sporniket/kicad-conversions--thomson-mo5--v1/references/motherboard/bottom-reversed.png

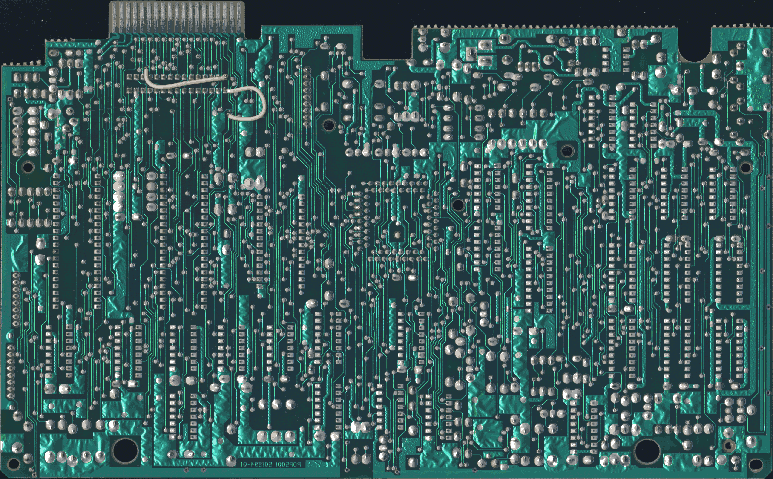
references/motherboard/bottom-reversed.png
