sporniket/kicad-conversions--thomson-mo5--v1/references/motherboard/pictures_top/DSC_1524.JPG

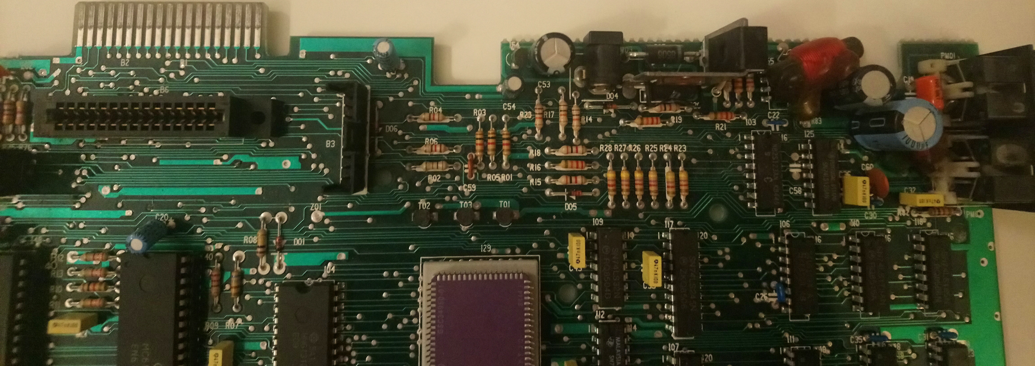
references/motherboard/pictures_top/DSC_1524.JPG
