sporniket/kicad-conversions--thomson-mo5--v1/references/motherboard/pictures_top/DSC_1542.JPG

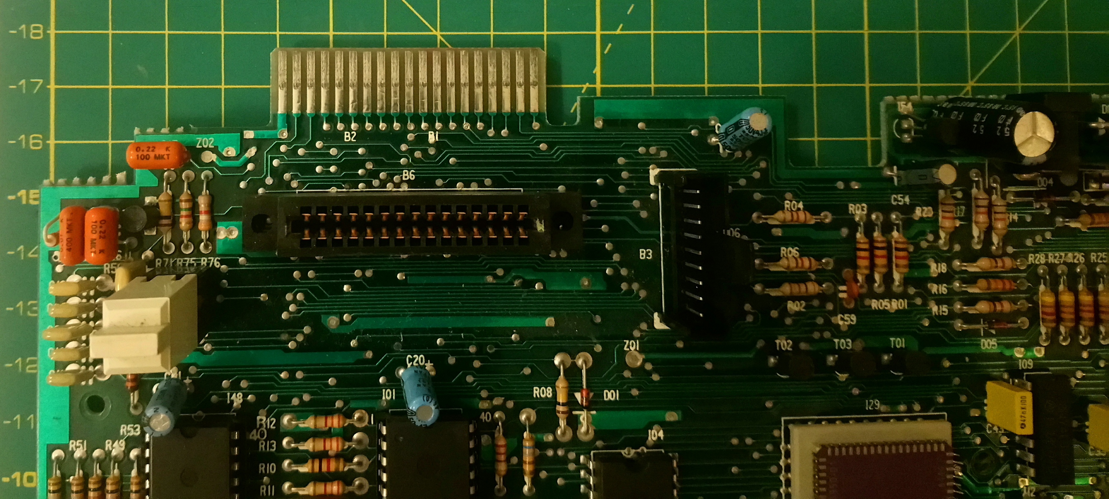
references/motherboard/pictures_top/DSC_1542.JPG
