sporniket/kicad-conversions--thomson-mo5--v1/references/motherboard/pictures_top/DSC_1543.JPG

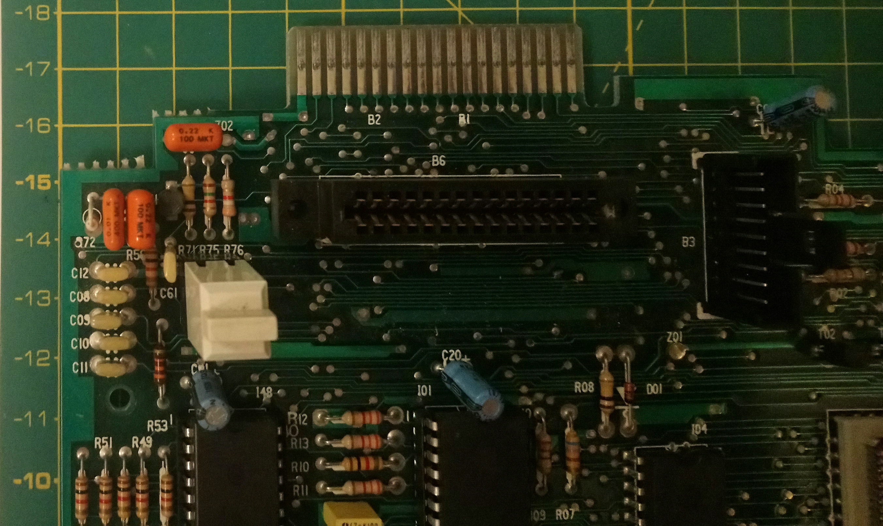
references/motherboard/pictures_top/DSC_1543.JPG
