sporniket/kicad-conversions--thomson-mo5--v1/references/motherboard/top.png

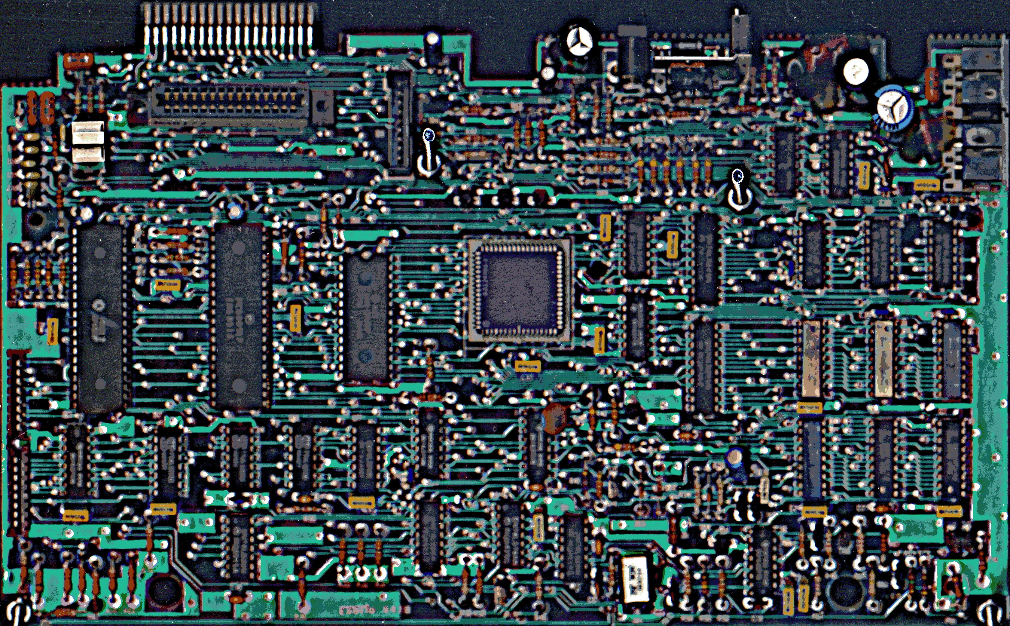
references/motherboard/top.png
