sporniket/kicad-conversions--thomson-mo5--v1/subsheet_100.kicad_sch

## KiCad design subsheet_100.kicad_sch (2025-02-01, an earlier design)

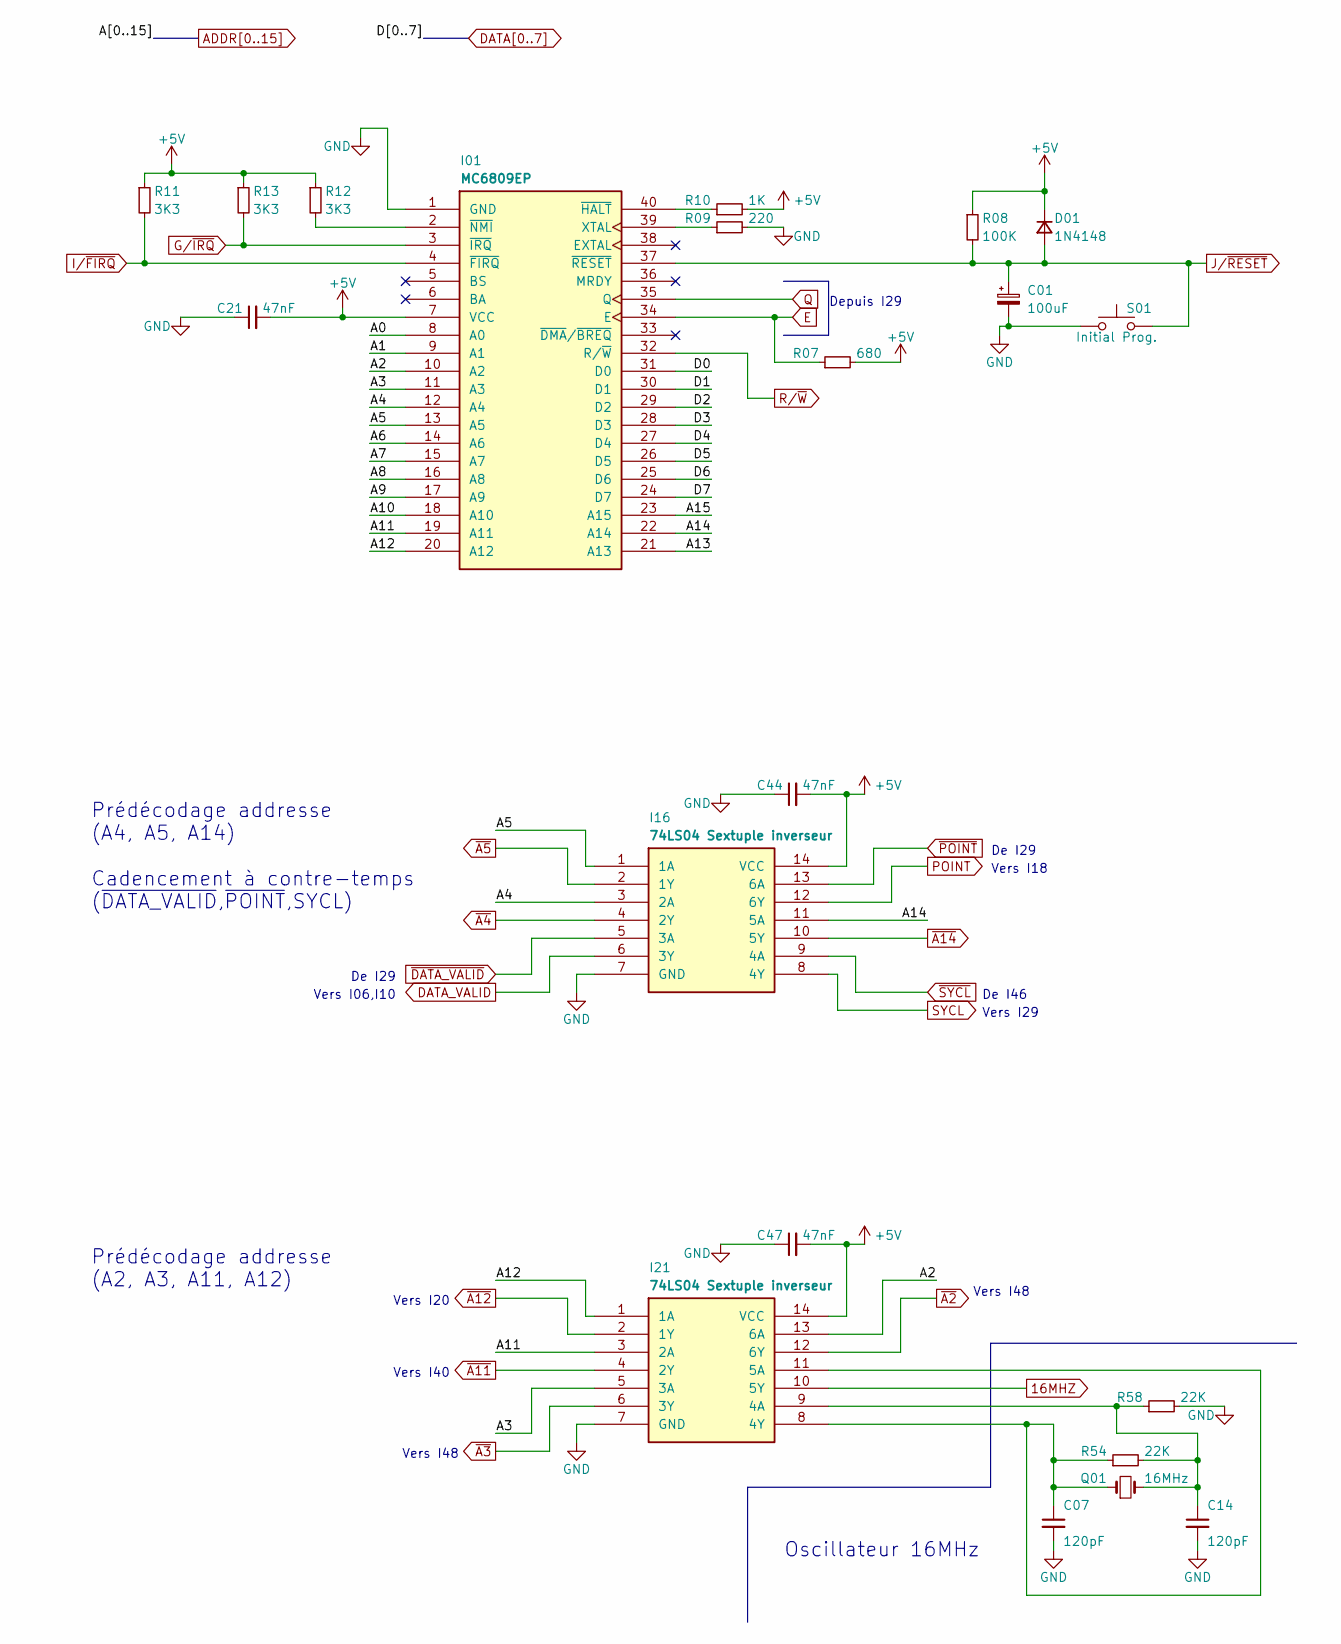
[picture p26: schematic subsheet_100.kicad_sch]

Parts:
C01: 100uF; Passive_THT_capacitor_polarized_EU_W2.54mm_L5.08mm
C07, C14: 120pF; Passive_THT_capacitor_mlcc_W2.54mm_L5.08mm
C21, C44, C47: 47nF; Passive_THT_capacitor_mlcc_W2.54mm_L5.08mm
D01: 1N4148; Passive_THT_diode_W2.54mm_L12.70mm
I01: MC6809EP; DIP-40_W15.24mm_LongPads
I16, I21: 74LS04 Sextuple inverseur; DIP-14_W7.62mm_LongPads
Q01: 16MHz
R07: 680; Passive_THT_resistor_EU_W2.54mm_L12.70mm
R08: 100K; Passive_THT_resistor_EU_W2.54mm_L12.70mm
R09: 220; Passive_THT_resistor_EU_W2.54mm_L12.70mm
R10: 1K; Passive_THT_resistor_EU_W2.54mm_L12.70mm
R11, R12, R13: 3K3; Passive_THT_resistor_EU_W2.54mm_L12.70mm
R54, R58: 22K; Passive_THT_resistor_EU_W2.54mm_L12.70mm
S01: Initial Prog.

Connections:
16MHZ: I21.10 (5Y)
+5V: C21.2, C44.2, C47.2, D01.1 (K), I01.7 (VCC), I16.14 (VCC), I21.14 (VCC), R07.2, R08.1, R10.2, R11.1, R12.1, R13.1
A0: I01.8 (A0)
A1: I01.9 (A1)
A2: I01.10 (A2), I21.13 (6A)
A3: I01.11 (A3), I21.5 (3A)
A4: I01.12 (A4), I16.3 (2A)
A5: I01.13 (A5), I16.1 (1A)
A6: I01.14 (A6)
A7: I01.15 (A7)
A8: I01.16 (A8)
A9: I01.17 (A9)
A10: I01.18 (A10)
A11: I01.19 (A11), I21.3 (2A)
A12: I01.20 (A12), I21.1 (1A)
A13: I01.21 (A13)
A14: I01.22 (A14), I16.11 (5A)
A15: I01.23 (A15)
D0: I01.31 (D0)
D1: I01.30 (D1)
D2: I01.29 (D2)
D3: I01.28 (D3)
D4: I01.27 (D4)
D5: I01.26 (D5)
D6: I01.25 (D6)
D7: I01.24 (D7)
DATA_VALID: I16.6 (3Y)
E: I01.34 (E), R07.1
GND: C01.2, C07.2, C14.2, C21.1, C44.1, C47.1, I01.1 (GND), I16.7 (GND), I21.7 (GND), R09.2, R58.2, S01.1
G/~IRQ: I01.3 (~IRQ), R13.2
I/~FIRQ: I01.4 (~FIRQ), R11.2
J/~RESET: C01.1, D01.2 (A), I01.37 (~RESET), R08.2, S01.2
unnamed: C07.1, I21.8 (4Y), I21.11 (5A), Q01.1, R54.1
unnamed: C14.1, I21.9 (4A), Q01.2, R54.2, R58.1
unnamed: I01.2 (~NMI), R12.2
unnamed: I01.39 (XTAL), R09.1
unnamed: I01.40 (~HALT), R10.1
POINT: I16.12 (6Y)
Q: I01.35 (Q)
R/~W: I01.32 (R/~W)
SYCL: I16.8 (4Y)
~A2: I21.12 (6Y)
~A3: I21.6 (3Y)
~A4: I16.4 (2Y)
~A5: I16.2 (1Y)
~A11: I21.4 (2Y)
~A12: I21.2 (1Y)
~A14: I16.10 (5Y)
~DATA_VALID: I16.5 (3A)
~POINT: I16.13 (6A)
~SYCL: I16.9 (4A)

Notes on the sheet:
De I46
Vers I29
Vers I48
Vers I20
Oscillateur 16MHz
De I29
Prédécodage addresse (A2, A3, A11, A12)
Vers I06,I10
Vers I40
Prédécodage addresse (A4, A5, A14) Cadencement à contre-temps (~{DATA_VALID},~{POINT},SYCL)
Depuis I29
Vers I18
