sporniket/kicad-conversions--thomson-mo5--v1/subsheet_101.kicad_sch

## KiCad design subsheet_101.kicad_sch (2024-12-30, an earlier design)

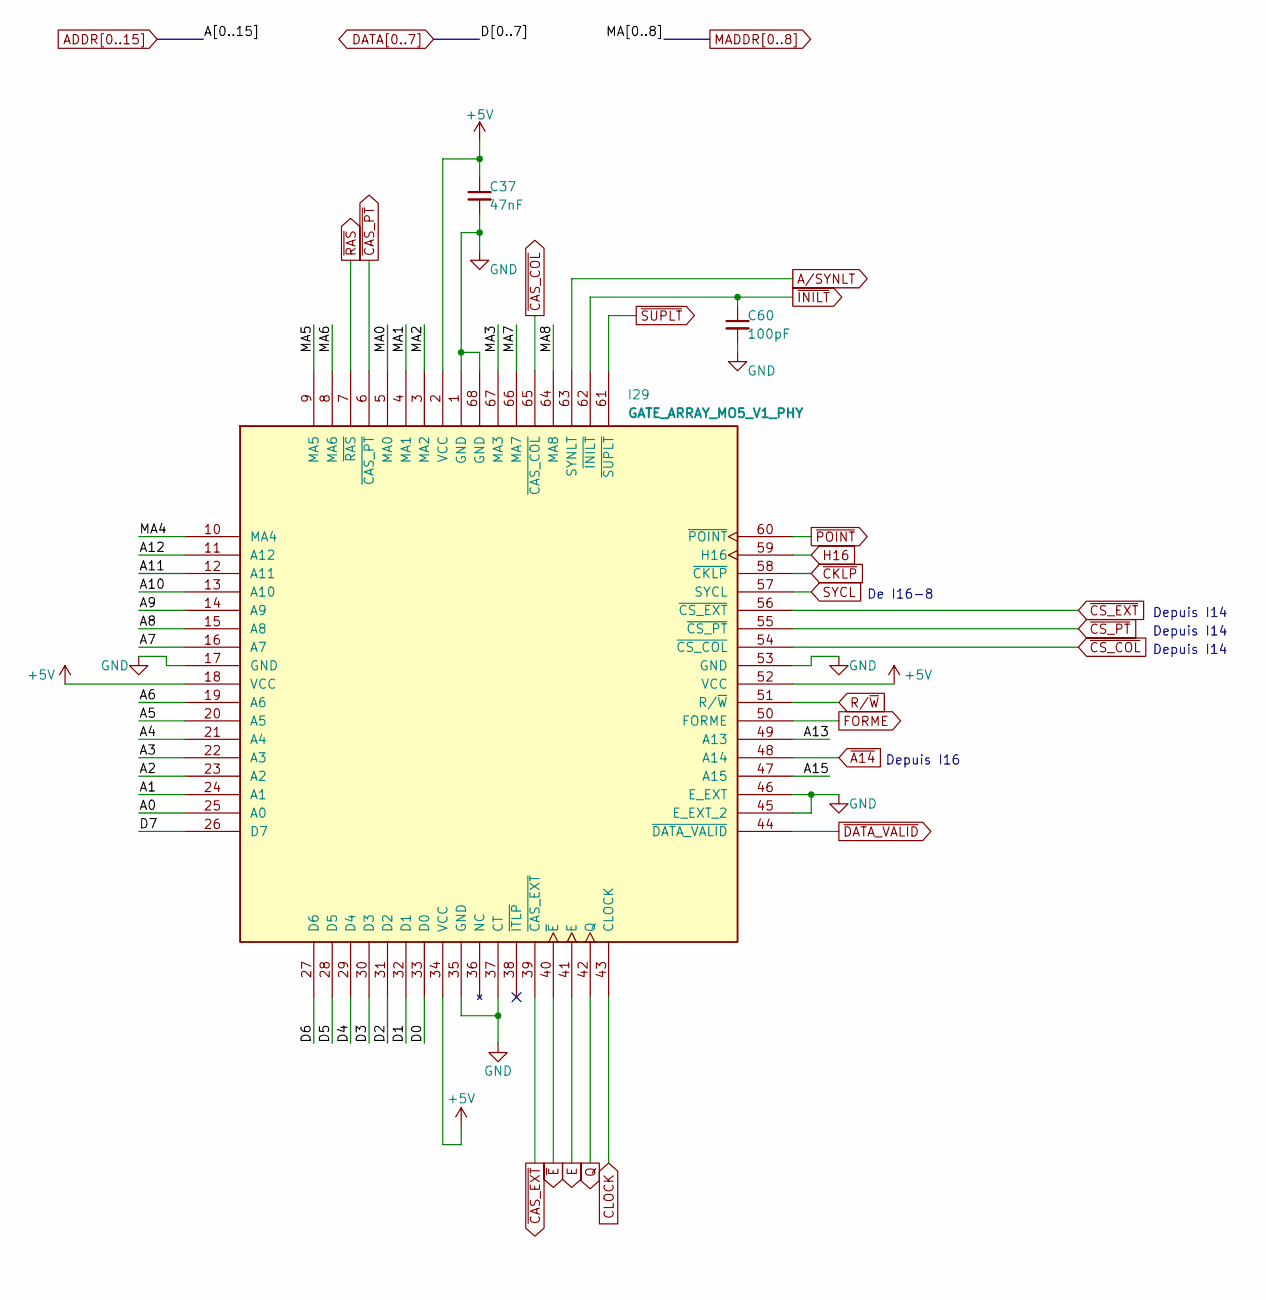
[picture p27: schematic subsheet_101.kicad_sch]

Parts:
C37: 47nF; Passive_THT_capacitor_mlcc_W2.54mm_L5.08mm
C60: 100pF; Passive_THT_capacitor_mlcc_W2.54mm_L5.08mm
I29: GATE_ARRAY_MO5_V1_PHY; gate_array_plcc68_staggered_with_key_hole

Connections:
+5V: C37.1, I29.2 (VCC), I29.18 (VCC), I29.34 (VCC), I29.52 (VCC)
A0: I29.25 (A0)
A1: I29.24 (A1)
A2: I29.23 (A2)
A3: I29.22 (A3)
A4: I29.21 (A4)
A5: I29.20 (A5)
A6: I29.19 (A6)
A7: I29.16 (A7)
A8: I29.15 (A8)
A9: I29.14 (A9)
A10: I29.13 (A10)
A11: I29.12 (A11)
A12: I29.11 (A12)
A13: I29.49 (A13)
A15: I29.47 (A15)
A/SYNLT: I29.63 (SYNLT)
CLOCK: I29.43 (CLOCK)
D0: I29.33 (D0)
D1: I29.32 (D1)
D2: I29.31 (D2)
D3: I29.30 (D3)
D4: I29.29 (D4)
D5: I29.28 (D5)
D6: I29.27 (D6)
D7: I29.26 (D7)
E: I29.41 (E)
FORME: I29.50 (FORME)
GND: C37.2, C60.2, I29.1 (GND), I29.17 (GND), I29.35 (GND), I29.37 (CT), I29.45 (E_EXT_2), I29.46 (E_EXT), I29.53 (GND), I29.68 (GND)
H16: I29.59 (H16)
MA0: I29.5 (MA0)
MA1: I29.4 (MA1)
MA2: I29.3 (MA2)
MA3: I29.67 (MA3)
MA4: I29.10 (MA4)
MA5: I29.9 (MA5)
MA6: I29.8 (MA6)
MA7: I29.66 (MA7)
MA8: I29.64 (MA8)
Q: I29.42 (Q)
R/~W: I29.51 (R/~W)
SYCL: I29.57 (SYCL)
~A14: I29.48 (A14)
~CAS_COL: I29.65 (~CAS_COL)
~CAS_EXT: I29.39 (~CAS_EXT)
~CAS_PT: I29.6 (~CAS_PT)
~CKLP: I29.58 (~CKLP)
~CS_COL: I29.54 (~CS_COL)
~CS_EXT: I29.56 (~CS_EXT)
~CS_PT: I29.55 (~CS_PT)
~DATA_VALID: I29.44 (~DATA_VALID)
~E: I29.40 (~E)
~INILT: C60.1, I29.62 (~INILT)
~POINT: I29.60 (~POINT)
~RAS: I29.7 (~RAS)
~SUPLT: I29.61 (~SUPLT)

Notes on the sheet:
Depuis I14
Depuis I16
De I16-8
