sporniket/kicad-conversions--thomson-mo5--v1/subsheet_102.kicad_sch

## KiCad design subsheet_102.kicad_sch (2024-12-30, an earlier design)

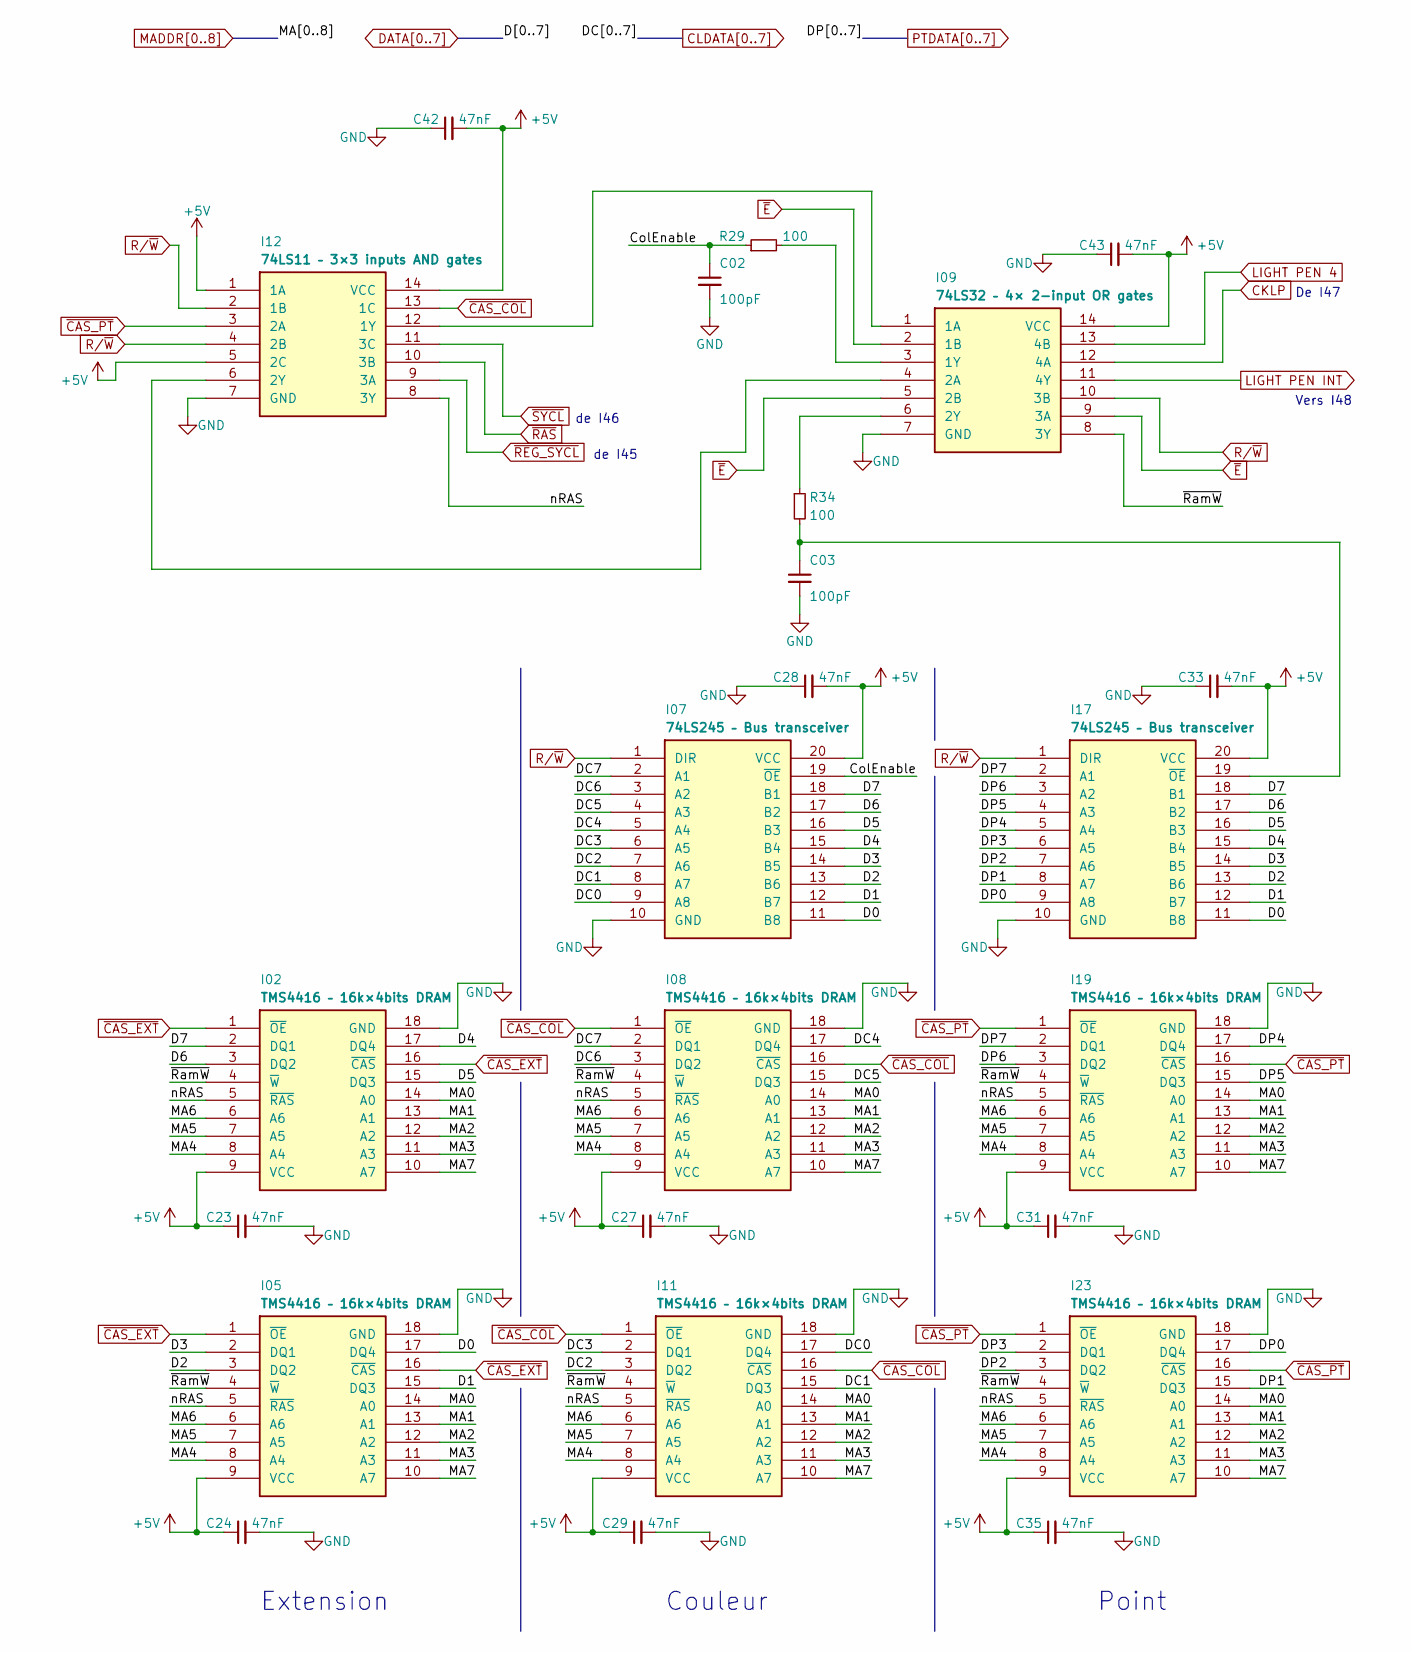
[picture p28: schematic subsheet_102.kicad_sch]

Parts:
C02, C03: 100pF; Passive_THT_capacitor_mlcc_W2.54mm_L5.08mm
C23, C24, C27, C28, C29, C31, C33, C35, C42, C43: 47nF; Passive_THT_capacitor_mlcc_W2.54mm_L5.08mm
I02, I05, I08, I11, I19, I23: TMS4416 – 16k×4bits DRAM; DIP-18_W7.62mm_LongPads
I07, I17: 74LS245 – Bus transceiver; DIP-20_W7.62mm_LongPads
I09: 74LS32 – 4× 2-input OR gates; DIP-14_W7.62mm_LongPads
I12: 74LS11 – 3×3 inputs AND gates; DIP-14_W7.62mm_LongPads
R29, R34: 100; Passive_THT_resistor_EU_W2.54mm_L12.70mm

Connections:
+5V: C23.1, C24.1, C27.1, C28.2, C29.1, C31.1, C33.2, C35.1, C42.2, C43.2, I02.9 (VCC), I05.9 (VCC), I07.20 (VCC), I08.9 (VCC), I09.14 (VCC), I11.9 (VCC), I12.1 (1A), I12.5 (2C), I12.14 (VCC), I17.20 (VCC), I19.9 (VCC), I23.9 (VCC)
CKLP: I09.12 (4A)
ColEnable: C02.1, I07.19 (~OE), R29.1
D0: I05.17 (DQ4), I07.11 (B8), I17.11 (B8)
D1: I05.15 (DQ3), I07.12 (B7), I17.12 (B7)
D2: I05.3 (DQ2), I07.13 (B6), I17.13 (B6)
D3: I05.2 (DQ1), I07.14 (B5), I17.14 (B5)
D4: I02.17 (DQ4), I07.15 (B4), I17.15 (B4)
D5: I02.15 (DQ3), I07.16 (B3), I17.16 (B3)
D6: I02.3 (DQ2), I07.17 (B2), I17.17 (B2)
D7: I02.2 (DQ1), I07.18 (B1), I17.18 (B1)
DC0: I07.9 (A8), I11.17 (DQ4)
DC1: I07.8 (A7), I11.15 (DQ3)
DC2: I07.7 (A6), I11.3 (DQ2)
DC3: I07.6 (A5), I11.2 (DQ1)
DC4: I07.5 (A4), I08.17 (DQ4)
DC5: I07.4 (A3), I08.15 (DQ3)
DC6: I07.3 (A2), I08.3 (DQ2)
DC7: I07.2 (A1), I08.2 (DQ1)
DP0: I17.9 (A8), I23.17 (DQ4)
DP1: I17.8 (A7), I23.15 (DQ3)
DP2: I17.7 (A6), I23.3 (DQ2)
DP3: I17.6 (A5), I23.2 (DQ1)
DP4: I17.5 (A4), I19.17 (DQ4)
DP5: I17.4 (A3), I19.15 (DQ3)
DP6: I17.3 (A2), I19.3 (DQ2)
DP7: I17.2 (A1), I19.2 (DQ1)
GND: C02.2, C03.2, C23.2, C24.2, C27.2, C28.1, C29.2, C31.2, C33.1, C35.2, C42.1, C43.1, I02.18 (GND), I05.18 (GND), I07.10 (GND), I08.18 (GND), I09.7 (GND), I11.18 (GND), I12.7 (GND), I17.10 (GND), I19.18 (GND), I23.18 (GND)
LIGHT PEN 4: I09.13 (4B)
LIGHT PEN INT: I09.11 (4Y)
MA0: I02.14 (A0), I05.14 (A0), I08.14 (A0), I11.14 (A0), I19.14 (A0), I23.14 (A0)
MA1: I02.13 (A1), I05.13 (A1), I08.13 (A1), I11.13 (A1), I19.13 (A1), I23.13 (A1)
MA2: I02.12 (A2), I05.12 (A2), I08.12 (A2), I11.12 (A2), I19.12 (A2), I23.12 (A2)
MA3: I02.11 (A3), I05.11 (A3), I08.11 (A3), I11.11 (A3), I19.11 (A3), I23.11 (A3)
MA4: I02.8 (A4), I05.8 (A4), I08.8 (A4), I11.8 (A4), I19.8 (A4), I23.8 (A4)
MA5: I02.7 (A5), I05.7 (A5), I08.7 (A5), I11.7 (A5), I19.7 (A5), I23.7 (A5)
MA6: I02.6 (A6), I05.6 (A6), I08.6 (A6), I11.6 (A6), I19.6 (A6), I23.6 (A6)
MA7: I02.10 (A7), I05.10 (A7), I08.10 (A7), I11.10 (A7), I19.10 (A7), I23.10 (A7)
unnamed: C03.1, I17.19 (~OE), R34.2
unnamed: I09.1 (1A), I12.12 (1Y)
unnamed: I09.3 (1Y), R29.2
unnamed: I09.4 (2A), I12.6 (2Y)
unnamed: I09.6 (2Y), R34.1
R/~W: I07.1 (DIR), I09.10 (3B), I12.2 (1B), I12.4 (2B), I17.1 (DIR)
nRAS: I02.5 (~RAS), I05.5 (~RAS), I08.5 (~RAS), I11.5 (~RAS), I12.8 (3Y), I19.5 (~RAS), I23.5 (~RAS)
~CAS_COL: I08.1 (~OE), I08.16 (~CAS), I11.1 (~OE), I11.16 (~CAS), I12.13 (1C)
~CAS_EXT: I02.1 (~OE), I02.16 (~CAS), I05.1 (~OE), I05.16 (~CAS)
~CAS_PT: I12.3 (2A), I19.1 (~OE), I19.16 (~CAS), I23.1 (~OE), I23.16 (~CAS)
~E: I09.2 (1B), I09.5 (2B), I09.9 (3A)
~RAS: I12.10 (3B)
~REG_SYCL: I12.9 (3A)
~RamW: I02.4 (~W), I05.4 (~W), I08.4 (~W), I09.8 (3Y), I11.4 (~W), I19.4 (~W), I23.4 (~W)
~SYCL: I12.11 (3C)

Notes on the sheet:
Extension
Vers I48
de I45
De I47
Couleur
de I46
Point
