sporniket/kicad-conversions--thomson-mo5--v1/subsheet_103.kicad_sch

## KiCad design subsheet_103.kicad_sch (2024-12-30, an earlier design)

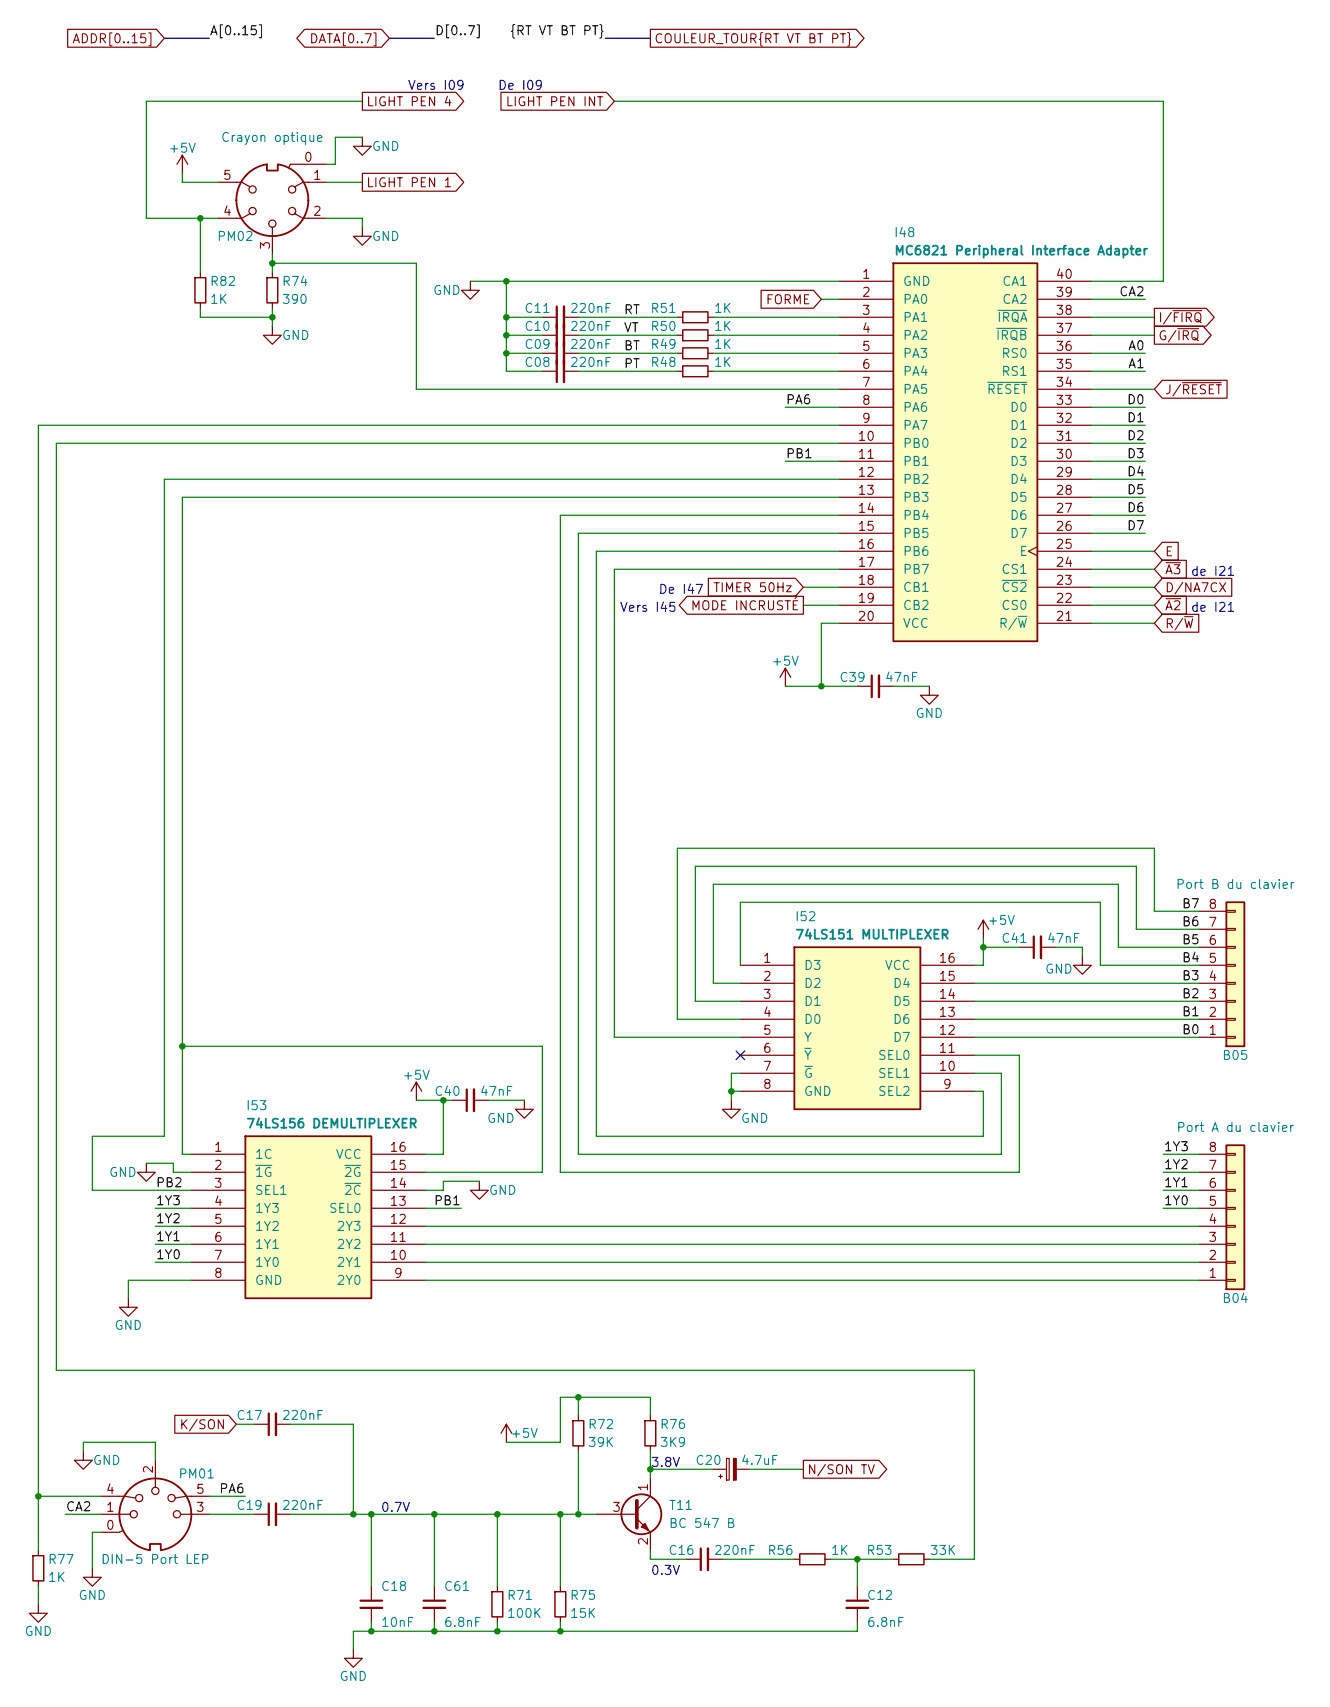
[picture p29: schematic subsheet_103.kicad_sch]

Parts:
B04: Port A du clavier
B05: Port B du clavier
C08, C09, C10, C11, C16, C17, C19: 220nF; Passive_THT_capacitor_mlcc_W2.54mm_L5.08mm
C12, C61: 6.8nF; Passive_THT_capacitor_mlcc_W2.54mm_L5.08mm
C18: 10nF; Passive_THT_capacitor_mlcc_W2.54mm_L5.08mm
C20: 4.7uF; Passive_THT_capacitor_polarized_EU_W2.54mm_L5.08mm
C39, C40, C41: 47nF; Passive_THT_capacitor_mlcc_W2.54mm_L5.08mm
I48: MC6821 Peripheral Interface Adapter; DIP-40_W15.24mm_LongPads
I52: 74LS151 MULTIPLEXER; DIP-16_W7.62mm_LongPads
I53: 74LS156 DEMULTIPLEXER; DIP-16_W7.62mm_LongPads
PM01: DIN-5 Port LEP
PM02: Crayon optique
R48, R49, R50, R51, R56, R77, R82: 1K; Passive_THT_resistor_EU_W2.54mm_L12.70mm
R53: 33K; Passive_THT_resistor_EU_W2.54mm_L12.70mm
R71: 100K; Passive_THT_resistor_EU_W2.54mm_L12.70mm
R72: 39K; Passive_THT_resistor_EU_W2.54mm_L5.08mm
R74: 390; Passive_THT_resistor_EU_W2.54mm_L12.70mm
R75: 15K; Passive_THT_resistor_EU_W2.54mm_L12.70mm
R76: 3K9; Passive_THT_resistor_EU_W2.54mm_L12.70mm
T11: BC 547 B; TO-92_Inline_Wide

Connections:
1Y0: B04.5, I53.7 (1Y0)
1Y1: B04.6, I53.6 (1Y1)
1Y2: B04.7, I53.5 (1Y2)
1Y3: B04.8, I53.4 (1Y3)
+5V: C39.1, C40.1, C41.1, I48.20 (VCC), I52.16 (VCC), I53.16 (VCC), PM02.5, R72.1, R76.1
A0: I48.36 (RS0)
A1: I48.35 (RS1)
B0: B05.1, I52.12 (D7)
B1: B05.2, I52.13 (D6)
B2: B05.3, I52.14 (D5)
B3: B05.4, I52.15 (D4)
B4: B05.5, I52.1 (D3)
B5: B05.6, I52.2 (D2)
B6: B05.7, I52.3 (D1)
B7: B05.8, I52.4 (D0)
BT: C09.2, R49.1
CA2: I48.39 (CA2), PM01.1
D0: I48.33 (D0)
D1: I48.32 (D1)
D2: I48.31 (D2)
D3: I48.30 (D3)
D4: I48.29 (D4)
D5: I48.28 (D5)
D6: I48.27 (D6)
D7: I48.26 (D7)
D/NA7CX: I48.23 (~CS2)
E: I48.25 (E)
FORME: I48.2 (PA0)
GND: C08.1, C09.1, C10.1, C11.1, C12.2, C18.2, C39.2, C40.2, C41.2, C61.2, I48.1 (GND), I52.7 (~G), I52.8 (GND), I53.2 (~1G), I53.8 (GND), I53.14 (~2C), PM01.0, PM01.2, PM02.0, PM02.2, R71.2, R74.2, R75.2, R77.2, R82.2
G/~IRQ: I48.37 (~IRQB)
I/~FIRQ: I48.38 (~IRQA)
J/~RESET: I48.34 (~RESET)
K/SON: C17.1
LIGHT PEN 1: PM02.1
LIGHT PEN 4: PM02.4, R82.1
LIGHT PEN INT: I48.40 (CA1)
MODE INCRUSTÉ: I48.19 (CB2)
unnamed: B04.1, I53.9 (2Y0)
unnamed: B04.2, I53.10 (2Y1)
unnamed: B04.3, I53.11 (2Y2)
unnamed: B04.4, I53.12 (2Y3)
unnamed: C12.1, R53.1, R56.2
unnamed: C16.1, T11.2 (E)
unnamed: C16.2, R56.1
unnamed: C17.2, C18.1, C19.2, C61.1, R71.1, R72.2, R75.1, T11.3 (B)
unnamed: C19.1, PM01.3
unnamed: C20.1, R76.2, T11.1 (C)
unnamed: I48.3 (PA1), R51.2
unnamed: I48.4 (PA2), R50.2
unnamed: I48.5 (PA3), R49.2
unnamed: I48.6 (PA4), R48.2
unnamed: I48.7 (PA5), PM02.3, R74.1
unnamed: I48.9 (PA7), PM01.4, R77.1
unnamed: I48.10 (PB0), R53.2
unnamed: I48.13 (PB3), I53.1 (1C), I53.15 (~2G)
unnamed: I48.14 (PB4), I52.11 (SEL0)
unnamed: I48.15 (PB5), I52.10 (SEL1)
unnamed: I48.16 (PB6), I52.9 (SEL2)
unnamed: I48.17 (PB7), I52.5 (Y)
N/SON TV: C20.2
PA6: I48.8 (PA6), PM01.5
PB1: I48.11 (PB1), I53.13 (SEL0)
PB2: I48.12 (PB2), I53.3 (SEL1)
PT: C08.2, R48.1
RT: C11.2, R51.1
R/~W: I48.21 (R/~W)
TIMER 50Hz: I48.18 (CB1)
VT: C10.2, R50.1
~A2: I48.22 (CS0)
~A3: I48.24 (CS1)

Notes on the sheet:
de I21
0.3V
De I47
3.8V
0.7V
Vers I45
Vers I09
De I09
