sporniket/kicad-conversions--thomson-mo5--v1/subsheet_104.kicad_sch

## KiCad design subsheet_104.kicad_sch (2024-12-30, an earlier design)

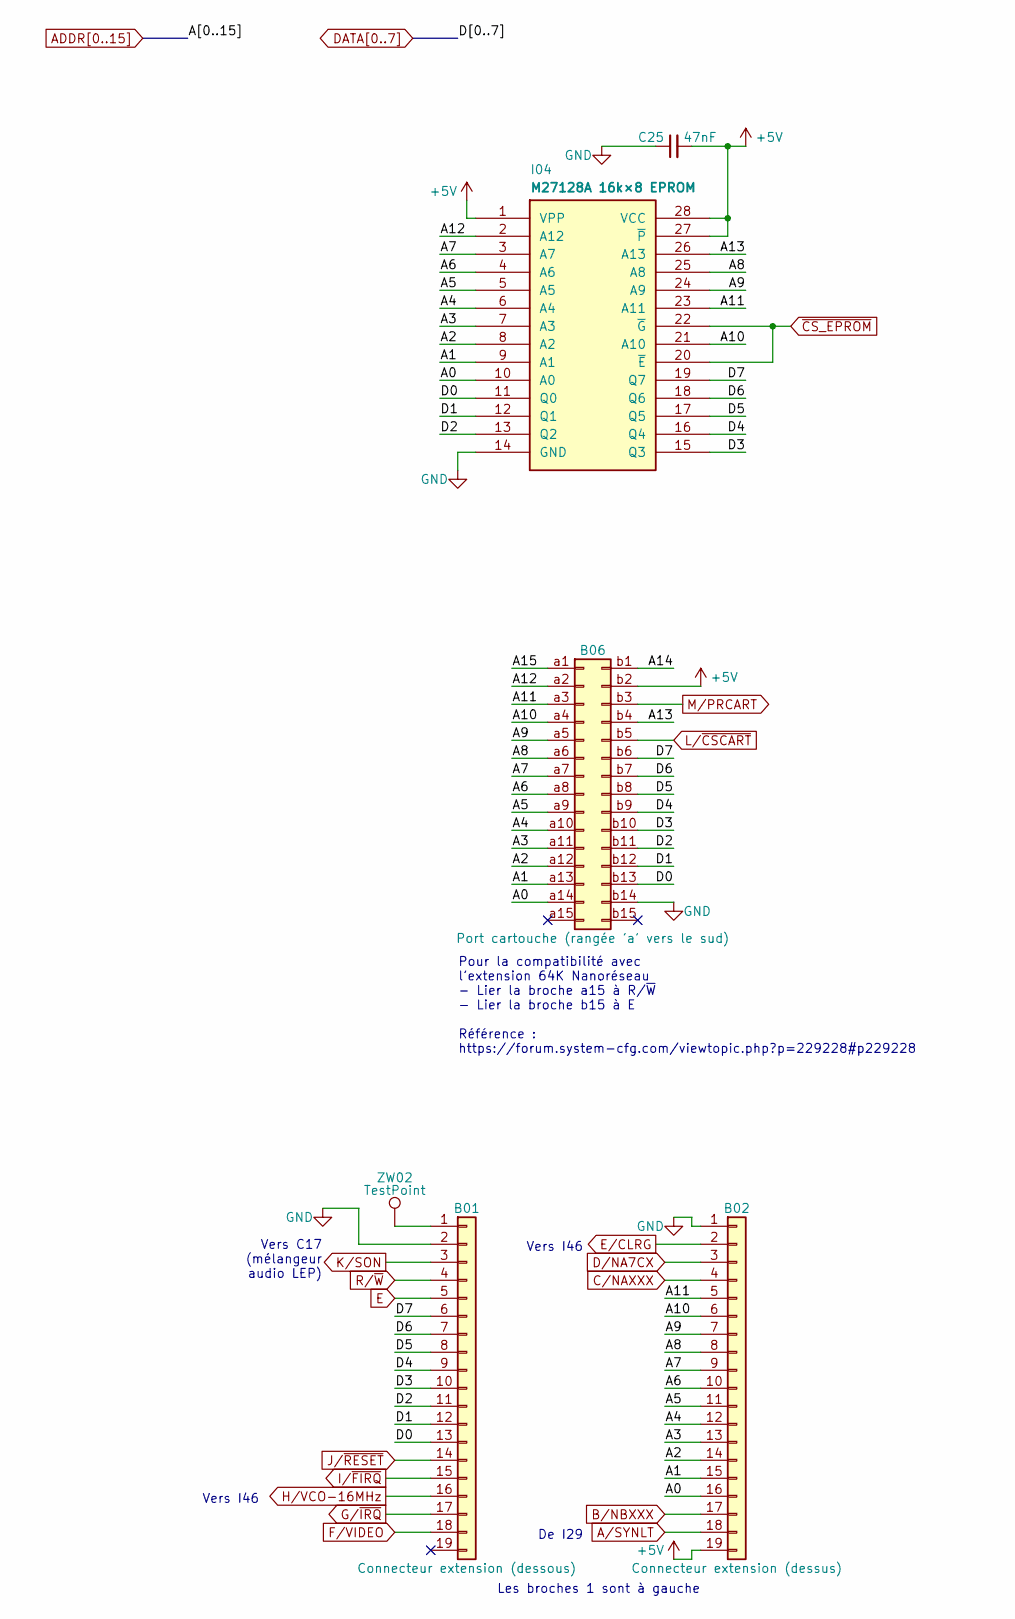
[picture p30: schematic subsheet_104.kicad_sch]

Parts:
B01: Connecteur extension (dessous); extension_port_1x19_backside_2mm_pad_width_2.54mm_pad_pitch
B02: Connecteur extension (dessus); extension_port_1x19_topside_2mm_pad_width_2.54mm_pad_pitch
B06: Port cartouche (rangée 'a' vers le sud); cartridge_port_2x13_pcb_edge_pitch_100mils_row_pitch_200mils
C25: 47nF; Passive_THT_capacitor_mlcc_W2.54mm_L5.08mm
I04: M27128A 16k×8 EPROM; DIP-28_W15.24mm_LongPads
ZW02: TestPoint; PinHeader_1x01_P2.54mm_Vertical

Connections:
+5V: B02.19, B06.b2, C25.2, I04.1 (VPP), I04.27 (~P), I04.28 (VCC)
A0: B02.16, B06.a14, I04.10 (A0)
A1: B02.15, B06.a13, I04.9 (A1)
A2: B02.14, B06.a12, I04.8 (A2)
A3: B02.13, B06.a11, I04.7 (A3)
A4: B02.12, B06.a10, I04.6 (A4)
A5: B02.11, B06.a9, I04.5 (A5)
A6: B02.10, B06.a8, I04.4 (A6)
A7: B02.9, B06.a7, I04.3 (A7)
A8: B02.8, B06.a6, I04.25 (A8)
A9: B02.7, B06.a5, I04.24 (A9)
A10: B02.6, B06.a4, I04.21 (A10)
A11: B02.5, B06.a3, I04.23 (A11)
A12: B06.a2, I04.2 (A12)
A13: B06.b4, I04.26 (A13)
A14: B06.b1
A15: B06.a1
A/SYNLT: B02.18
B/NBXXX: B02.17
C/NAXXX: B02.4
D0: B01.13, B06.b13, I04.11 (Q0)
D1: B01.12, B06.b12, I04.12 (Q1)
D2: B01.11, B06.b11, I04.13 (Q2)
D3: B01.10, B06.b10, I04.15 (Q3)
D4: B01.9, B06.b9, I04.16 (Q4)
D5: B01.8, B06.b8, I04.17 (Q5)
D6: B01.7, B06.b7, I04.18 (Q6)
D7: B01.6, B06.b6, I04.19 (Q7)
D/NA7CX: B02.3
E: B01.5
E/CLRG: B02.2
F/VIDEO: B01.18
GND: B01.2, B02.1, B06.b14, C25.1, I04.14 (GND)
G/~IRQ: B01.17
H/VCO-16MHz: B01.16
I/~FIRQ: B01.15
J/~RESET: B01.14
K/SON: B01.3
L/~CSCART: B06.b5
M/PRCART: B06.b3
unnamed: B01.1, ZW02.1
R/~W: B01.4
~CS_EPROM: I04.20 (~E), I04.22 (~G)

Notes on the sheet:
Vers I46
Les broches 1 sont à gauche
Pour la compatibilité avec l'extension 64K Nanoréseau - Lier la broche a15 à R/~{W} - Lier la broche b15 à E Référence : https://forum.system-cfg.com/viewtopic.php?p=229228#p229228
Vers C17 (mélangeur audio LEP)
De I29
