sporniket/kicad-conversions--thomson-mo5--v1/subsheet_105.kicad_sch

## KiCad design subsheet_105.kicad_sch (2024-12-30, an earlier design)

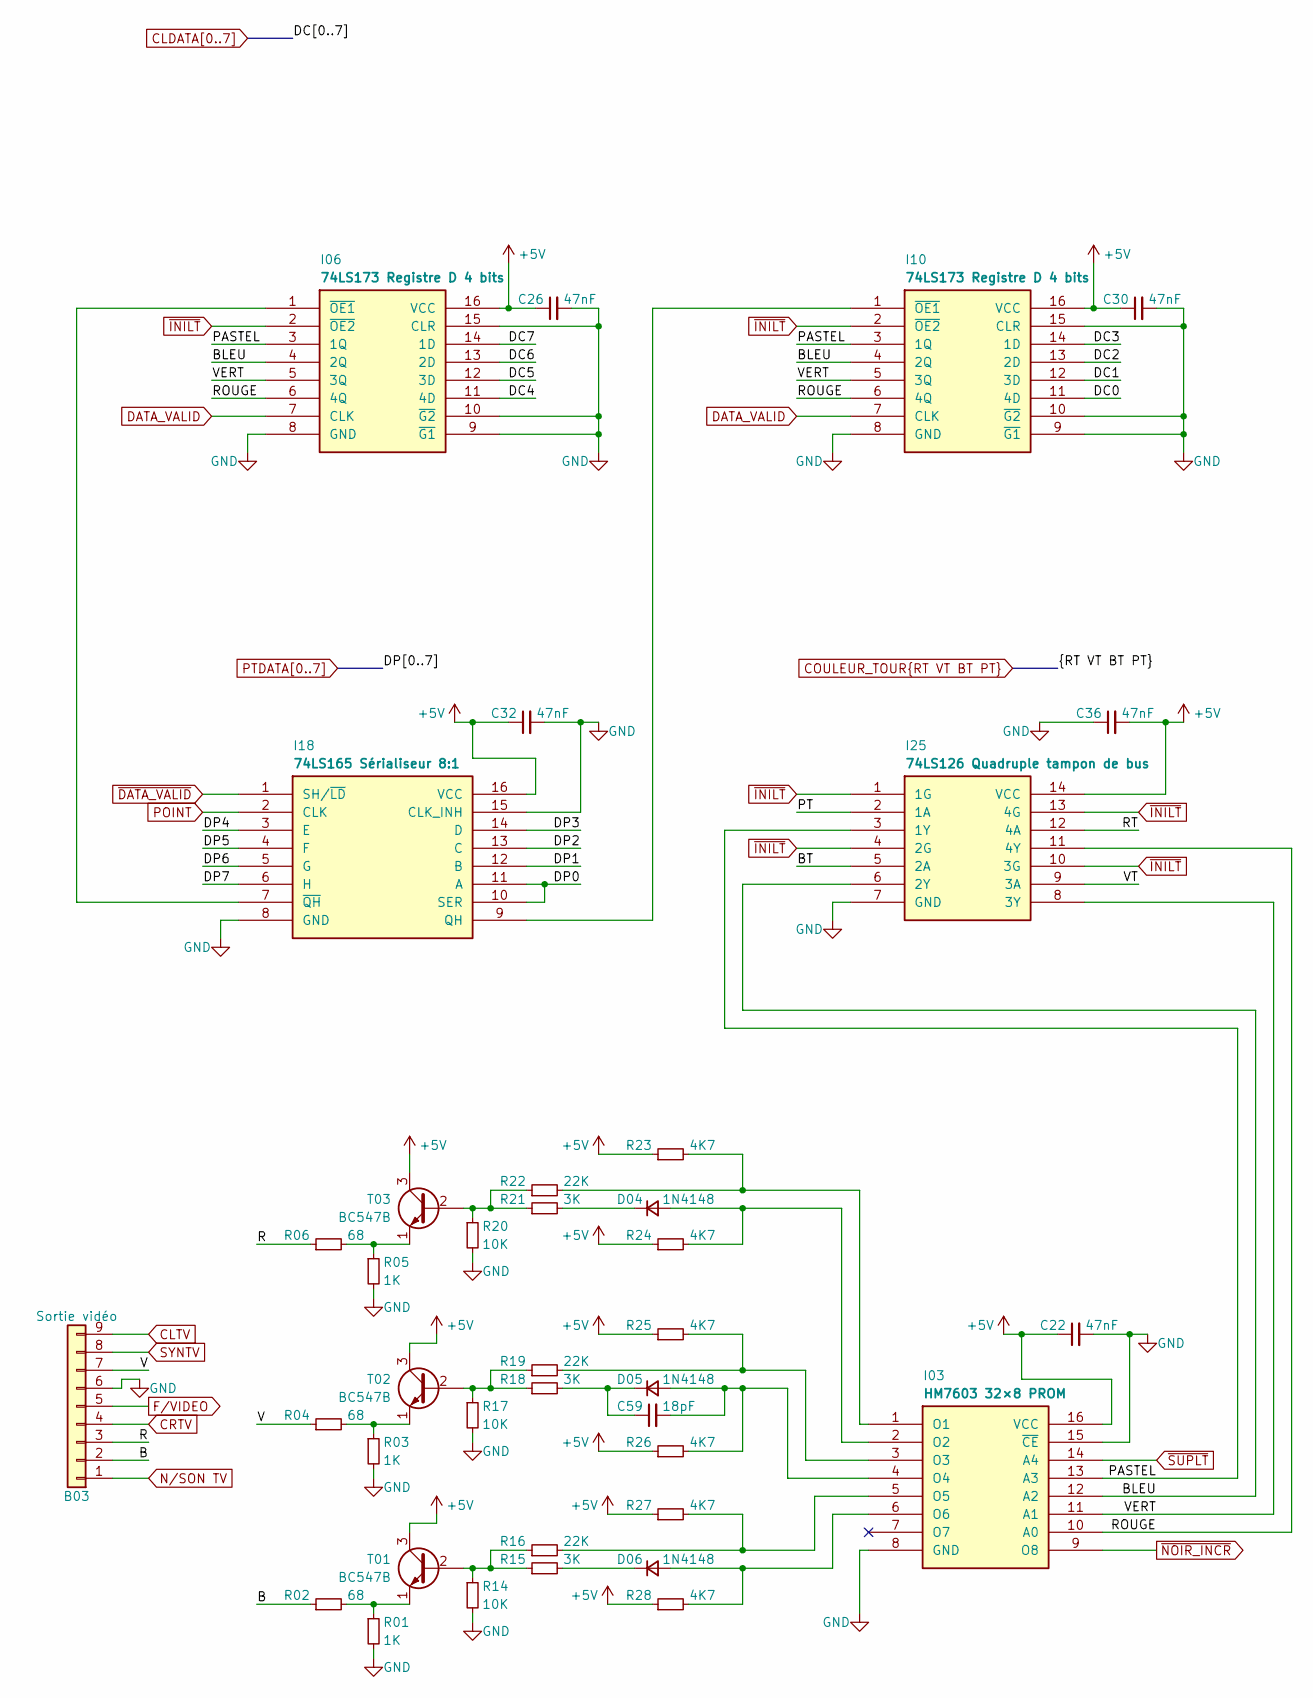
[picture p31: schematic subsheet_105.kicad_sch]

Parts:
B03: Sortie vidéo
C22, C26, C30, C32, C36: 47nF; Passive_THT_capacitor_mlcc_W2.54mm_L5.08mm
C59: 18pF; Passive_THT_capacitor_mlcc_W2.54mm_L5.08mm
D04, D05, D06: 1N4148; Passive_THT_diode_W2.54mm_L12.70mm
I03: HM7603 32×8 PROM; DIP-16_W7.62mm_LongPads
I06, I10: 74LS173 Registre D 4 bits; DIP-16_W7.62mm_LongPads
I18: 74LS165 Sérialiseur 8:1; DIP-16_W7.62mm_LongPads
I25: 74LS126 Quadruple tampon de bus; DIP-14_W7.62mm_LongPads
R01, R03, R05: 1K; Passive_THT_resistor_EU_W2.54mm_L12.70mm
R02, R04, R06: 68; Passive_THT_resistor_EU_W2.54mm_L12.70mm
R14, R17, R20: 10K; Passive_THT_resistor_EU_W2.54mm_L12.70mm
R15, R18, R21: 3K; Passive_THT_resistor_EU_W2.54mm_L12.70mm
R16, R19, R22: 22K; Passive_THT_resistor_EU_W2.54mm_L12.70mm
R23, R24, R25, R26, R27, R28: 4K7; Passive_THT_resistor_EU_W2.54mm_L12.70mm
T01, T02, T03: BC547B; TO-92_Inline_Wide

Connections:
+5V: C22.1, C26.1, C30.1, C32.1, C36.2, I03.16 (VCC), I06.16 (VCC), I10.16 (VCC), I18.16 (VCC), I25.14 (VCC), R23.1, R24.1, R25.1, R26.1, R27.1, R28.1, T01.3 (C), T02.3 (C), T03.3 (C)
B: B03.2, R02.1
BLEU: I03.12 (A2), I06.4 (2Q), I10.4 (2Q), I25.6 (2Y)
BT: I25.5 (2A)
CLTV: B03.9
CRTV: B03.4
DATA_VALID: I06.7 (CLK), I10.7 (CLK)
DC0: I10.11 (4D)
DC1: I10.12 (3D)
DC2: I10.13 (2D)
DC3: I10.14 (1D)
DC4: I06.11 (4D)
DC5: I06.12 (3D)
DC6: I06.13 (2D)
DC7: I06.14 (1D)
DP0: I18.10 (SER), I18.11 (A)
DP1: I18.12 (B)
DP2: I18.13 (C)
DP3: I18.14 (D)
DP4: I18.3 (E)
DP5: I18.4 (F)
DP6: I18.5 (G)
DP7: I18.6 (H)
F/VIDEO: B03.5
GND: B03.6, C22.2, C26.2, C30.2, C32.2, C36.1, I03.8 (GND), I03.15 (~CE), I06.8 (GND), I06.9 (~G1), I06.10 (~G2), I06.15 (CLR), I10.8 (GND), I10.9 (~G1), I10.10 (~G2), I10.15 (CLR), I18.8 (GND), I18.15 (CLK_INH), I25.7 (GND), R01.2, R03.2, R05.2, R14.2, R17.2, R20.2
unnamed: C59.1, D05.1 (K), R18.2
unnamed: C59.2, D05.2 (A), I03.4 (O4), R26.2
unnamed: D04.1 (K), R21.2
unnamed: D04.2 (A), I03.2 (O2), R24.2
unnamed: D06.1 (K), R15.2
unnamed: D06.2 (A), I03.6 (O6), R28.2
unnamed: I03.1 (O1), R22.2, R23.2
unnamed: I03.3 (O3), R19.2, R25.2
unnamed: I03.5 (O5), R16.2, R27.2
unnamed: I06.1 (~OE1), I18.7 (~QH)
unnamed: I10.1 (~OE1), I18.9 (QH)
unnamed: R01.1, R02.2, T01.1 (E)
unnamed: R03.1, R04.2, T02.1 (E)
unnamed: R05.1, R06.2, T03.1 (E)
unnamed: R14.1, R15.1, R16.1, T01.2 (B)
unnamed: R17.1, R18.1, R19.1, T02.2 (B)
unnamed: R20.1, R21.1, R22.1, T03.2 (B)
N/SON TV: B03.1
PASTEL: I03.13 (A3), I06.3 (1Q), I10.3 (1Q), I25.3 (1Y)
POINT: I18.2 (CLK)
PT: I25.2 (1A)
R: B03.3, R06.1
ROUGE: I03.10 (A0), I06.6 (4Q), I10.6 (4Q), I25.11 (4Y)
RT: I25.12 (4A)
SYNTV: B03.8
V: B03.7, R04.1
VERT: I03.11 (A1), I06.5 (3Q), I10.5 (3Q), I25.8 (3Y)
VT: I25.9 (3A)
~DATA_VALID: I18.1 (SH/~LD)
~INILT: I06.2 (~OE2), I10.2 (~OE2), I25.1 (1G), I25.4 (2G), I25.10 (3G), I25.13 (4G)
~NOIR_INCR: I03.9 (O8)
~SUPLT: I03.14 (A4)
