sporniket/kicad-conversions--thomson-mo5--v1/subsheet_106.kicad_sch

## KiCad design subsheet_106.kicad_sch (2024-12-30, an earlier design)

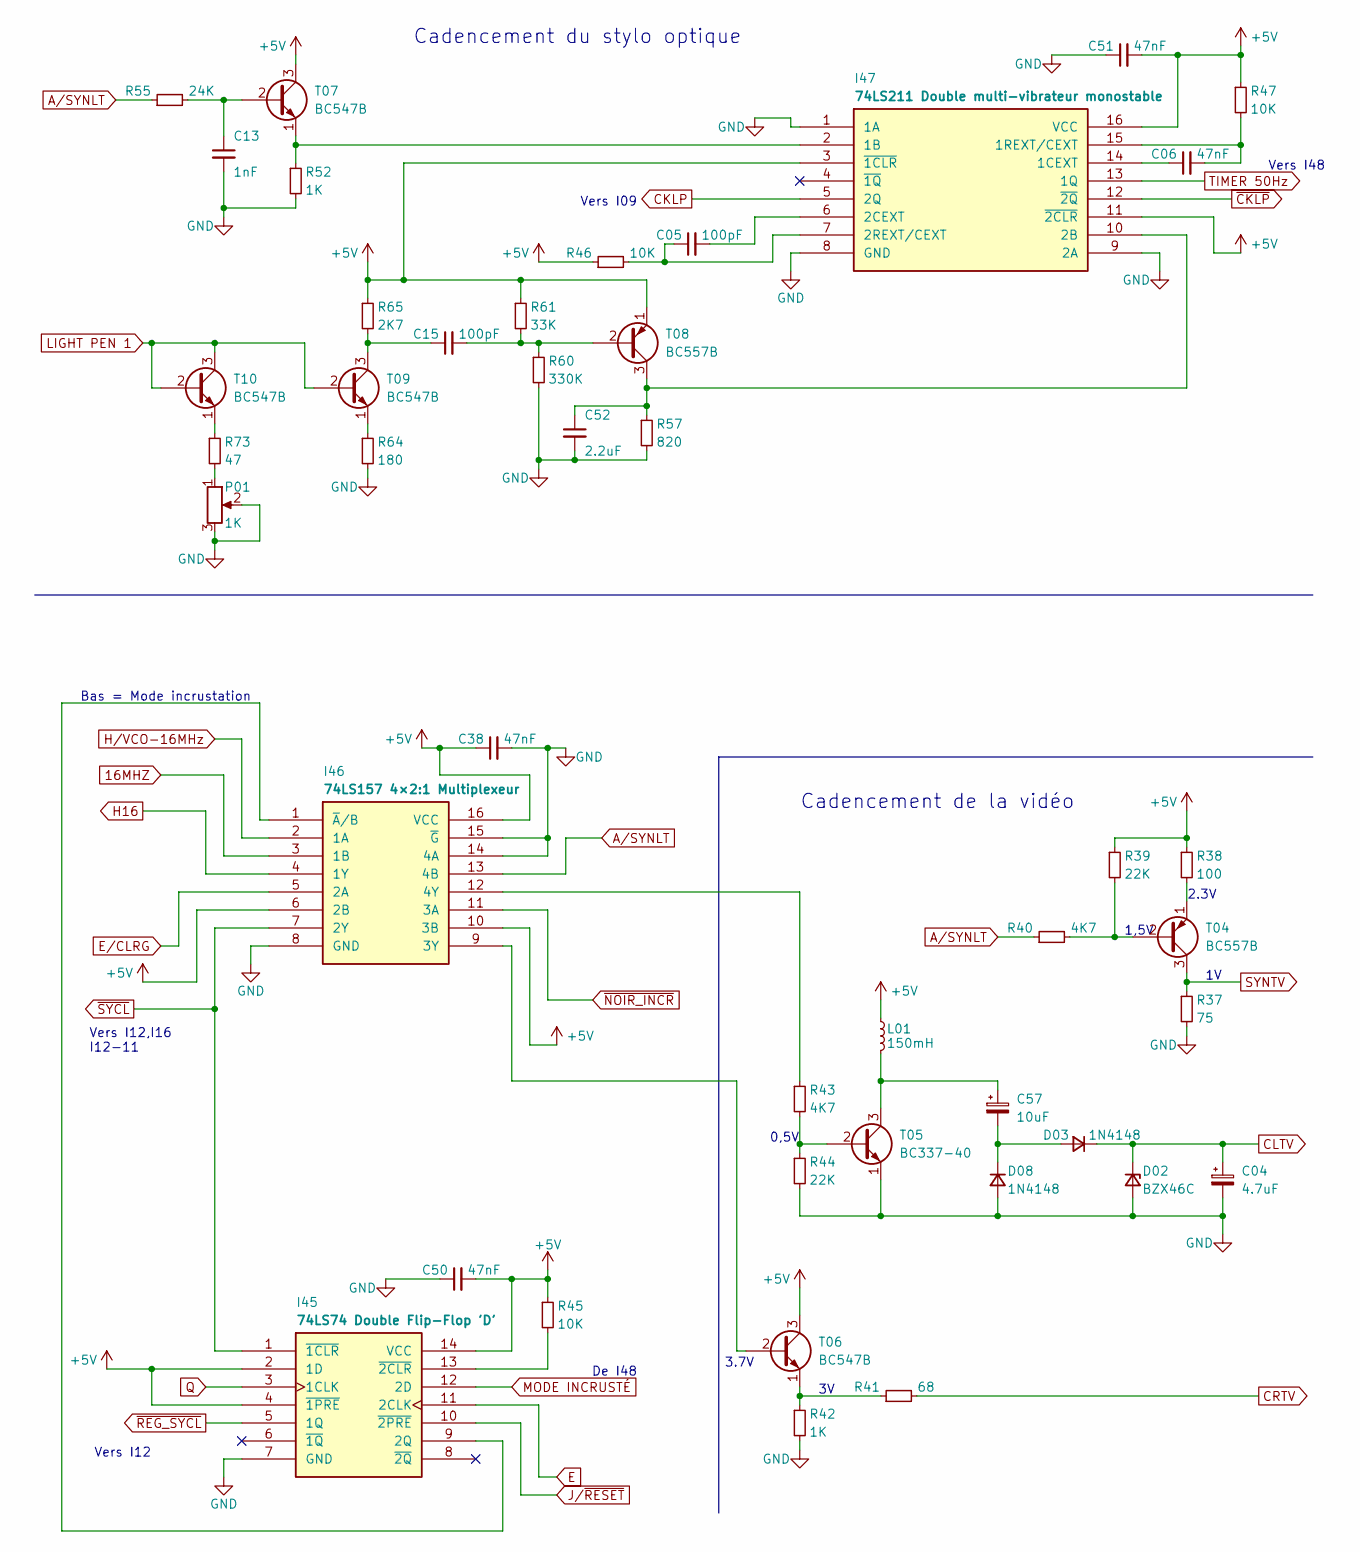
[picture p32: schematic subsheet_106.kicad_sch]

Parts:
C04: 4.7uF; Passive_THT_capacitor_polarized_EU_W2.54mm_L5.08mm
C05, C15: 100pF; Passive_THT_capacitor_mlcc_W2.54mm_L5.08mm
C06, C38, C50, C51: 47nF; Passive_THT_capacitor_mlcc_W2.54mm_L5.08mm
C13: 1nF; Passive_THT_capacitor_mlcc_W2.54mm_L5.08mm
C52: 2.2uF; Passive_THT_capacitor_mlcc_W2.54mm_L5.08mm
C57: 10uF; Passive_THT_capacitor_polarized_EU_W2.54mm_L5.08mm
D02: BZX46C; Passive_THT_diode_W2.54mm_L12.70mm
D03, D08: 1N4148; Passive_THT_diode_W2.54mm_L12.70mm
I45: 74LS74 Double Flip-Flop 'D'; DIP-14_W7.62mm_LongPads
I46: 74LS157 4×2:1 Multiplexeur; DIP-16_W7.62mm_LongPads
I47: 74LS211 Double multi-vibrateur monostable; DIP-16_W7.62mm_LongPads
L01: 150mH
P01: 1K
R37: 75; Passive_THT_resistor_EU_W2.54mm_L12.70mm
R38: 100; Passive_THT_resistor_EU_W2.54mm_L12.70mm
R39, R44: 22K; Passive_THT_resistor_EU_W2.54mm_L12.70mm
R40, R43: 4K7; Passive_THT_resistor_EU_W2.54mm_L12.70mm
R41: 68; Passive_THT_resistor_EU_W2.54mm_L12.70mm
R42, R52: 1K; Passive_THT_resistor_EU_W2.54mm_L12.70mm
R45, R46, R47: 10K; Passive_THT_resistor_EU_W2.54mm_L12.70mm
R55: 24K; Passive_THT_resistor_EU_W2.54mm_L12.70mm
R57: 820; Passive_THT_resistor_EU_W2.54mm_L12.70mm
R60: 330K; Passive_THT_resistor_EU_W2.54mm_L12.70mm
R61: 33K; Passive_THT_resistor_EU_W2.54mm_L12.70mm
R64: 180; Passive_THT_resistor_EU_W2.54mm_L12.70mm
R65: 2K7; Passive_THT_resistor_EU_W2.54mm_L12.70mm
R73: 47; Passive_THT_resistor_EU_W2.54mm_L12.70mm
T04, T08: BC557B; TO-92_Inline_Wide
T05: BC337-40; TO-92_Inline_Wide
T06, T07, T09, T10: BC547B; TO-92_Inline_Wide

Connections:
16MHZ: I46.3 (1B)
+5V: C38.1, C50.2, C51.2, I45.2 (1D), I45.4 (~1PRE), I45.14 (VCC), I46.6 (2B), I46.10 (3B), I46.16 (VCC), I47.3 (~1CLR), I47.11 (~2CLR), I47.16 (VCC), L01.1, R38.1, R39.1, R45.1, R46.1, R47.1, R61.1, R65.1, T06.3 (C), T07.3 (C), T08.1 (E)
A/SYNLT: I46.13 (4B), R40.1, R55.1
CKLP: I47.5 (2Q)
CLTV: C04.1, D02.1 (K), D03.1 (K)
CRTV: R41.2
E: I45.11 (2CLK)
E/CLRG: I46.5 (2A)
GND: C04.2, C13.2, C38.2, C50.1, C51.1, C52.2, D02.2 (A), D08.2 (A), I45.7 (GND), I46.8 (GND), I46.14 (4A), I46.15 (~G), I47.1 (1A), I47.8 (GND), I47.9 (2A), P01.2, P01.3, R37.2, R42.2, R44.2, R52.2, R57.2, R60.2, R64.2, T05.1 (E)
H16: I46.4 (1Y)
H/VCO-16MHz: I46.2 (1A)
J/~RESET: I45.10 (~2PRE)
LIGHT PEN 1: T09.2 (B), T10.2 (B), T10.3 (C)
MODE INCRUSTÉ: I45.12 (2D)
unnamed: C05.1, I47.7 (2REXT/CEXT), R46.2
unnamed: C05.2, I47.6 (2CEXT)
unnamed: C06.1, I47.14 (1CEXT)
unnamed: C06.2, I47.15 (1REXT/CEXT), R47.2
unnamed: C13.1, R55.2, T07.2 (B)
unnamed: C15.1, R65.2, T09.3 (C)
unnamed: C15.2, R60.1, R61.2, T08.2 (B)
unnamed: C52.1, I47.10 (2B), R57.1, T08.3 (C)
unnamed: C57.1, L01.2, T05.3 (C)
unnamed: C57.2, D03.2 (A), D08.1 (K)
unnamed: I45.9 (2Q), I46.1 (~A/B)
unnamed: I45.13 (~2CLR), R45.2
unnamed: I46.9 (3Y), T06.2 (B)
unnamed: I46.12 (4Y), R43.1
unnamed: I47.2 (1B), R52.1, T07.1 (E)
unnamed: P01.1, R73.2
unnamed: R38.2, T04.1 (E)
unnamed: R39.2, R40.2, T04.2 (B)
unnamed: R41.1, R42.1, T06.1 (E)
unnamed: R43.2, R44.1, T05.2 (B)
unnamed: R64.1, T09.1 (E)
unnamed: R73.1, T10.1 (E)
Q: I45.3 (1CLK)
SYNTV: R37.1, T04.3 (C)
TIMER 50Hz: I47.13 (1Q)
~CKLP: I47.12 (~2Q)
~NOIR_INCR: I46.11 (3A)
~REG_SYCL: I45.5 (1Q)
~SYCL: I45.1 (~1CLR), I46.7 (2Y)

Notes on the sheet:
3.7V
Cadencement de la vidéo
Vers I09
2.3V
0,5V
De I48
1,5V
Vers I48
Cadencement du stylo optique
Vers I12,I16 I12-11
Vers I12
Bas = Mode incrustation
