sporniket/kicad-conversions--thomson-mo5--v1/subsheet_107.kicad_sch

## KiCad design subsheet_107.kicad_sch (2024-12-30, an earlier design)

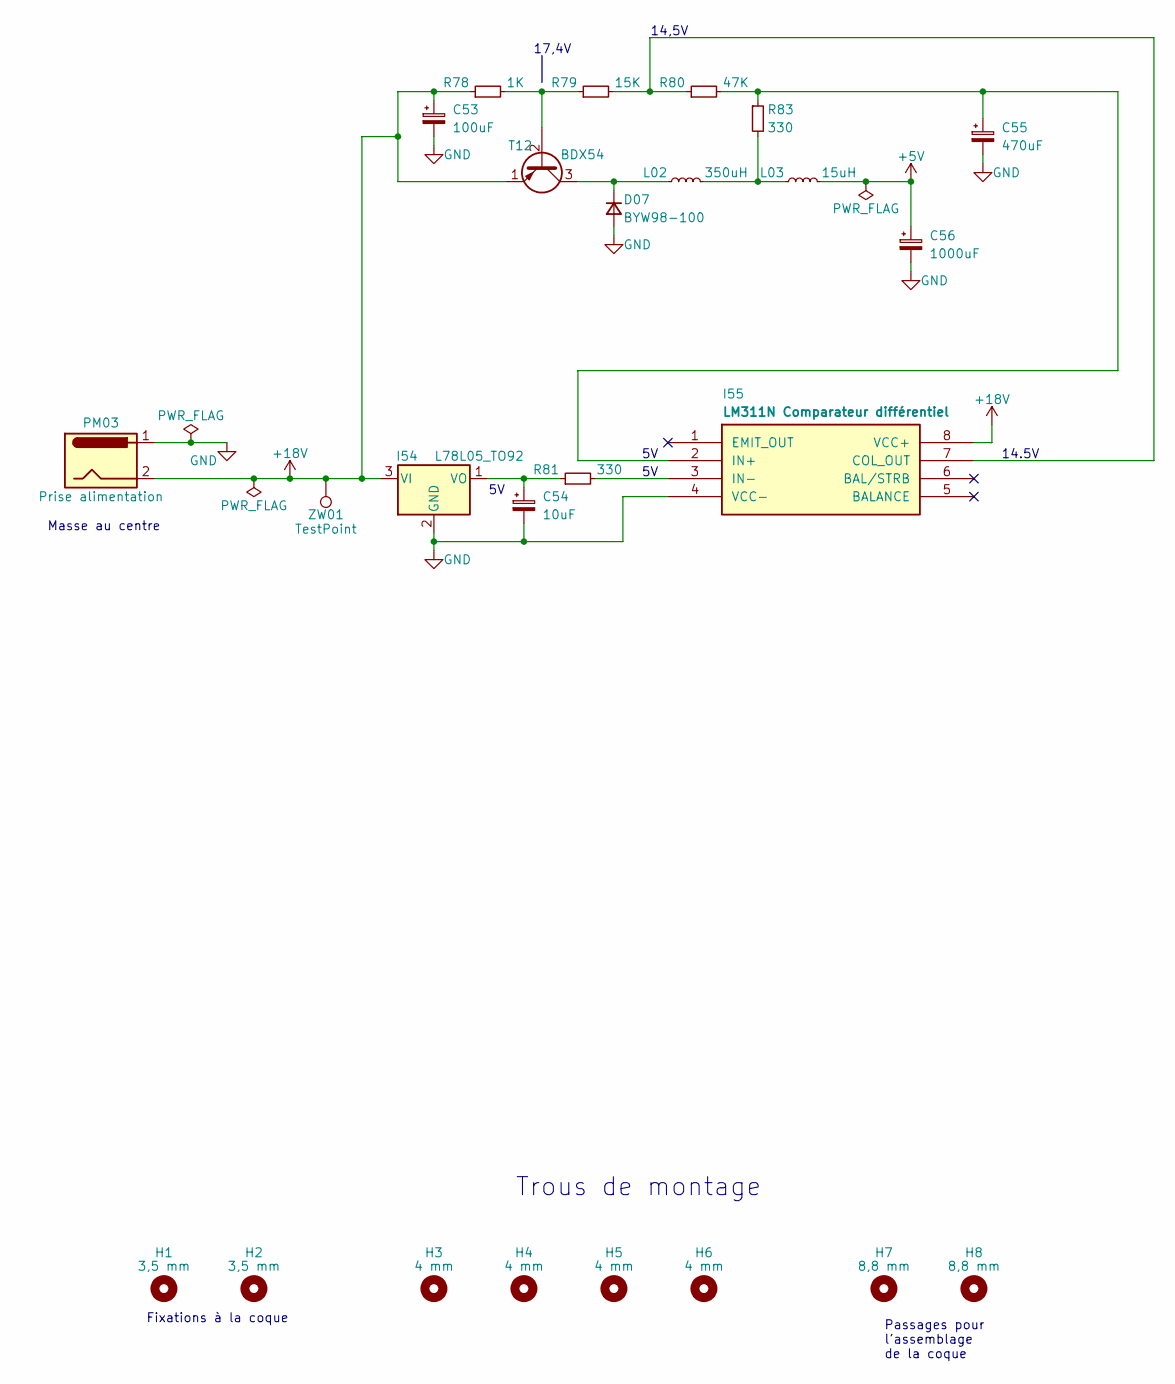
[picture p33: schematic subsheet_107.kicad_sch]

Parts:
C53: 100uF; Passive_THT_capacitor_polarized_EU_W2.54mm_L5.08mm
C54: 10uF; Passive_THT_capacitor_polarized_EU_W2.54mm_L5.08mm
C55: 470uF; CP_Radial_D10.0mm_P5.00mm
C56: 1000uF; CP_Radial_D13.0mm_P5.00mm
D07: BYW98-100; Passive_THT_diode_power_W5.715mm_L17.78mm
H1, H2: 3,5 mm; MountingHole_3.5mm_limited_courtyard
H3, H4, H5, H6: 4 mm; MountingHole_4mm_limited_courtyard
H7, H8: 8,8 mm; MountingHole_8.8mm_limited_courtyard
I54: L78L05_TO92; TO-92_Inline
I55: LM311N Comparateur différentiel; DIP-8_W7.62mm_LongPads
L02: 350uH
L03: 15uH
PM03: Prise alimentation
R78: 1K; Passive_THT_resistor_EU_W2.54mm_L12.70mm
R79: 15K; Passive_THT_resistor_EU_W2.54mm_L12.70mm
R80: 47K; Passive_THT_resistor_EU_W2.54mm_L12.70mm
R81, R83: 330; Passive_THT_resistor_EU_W2.54mm_L12.70mm
T12: BDX54; TO-92_Inline_Wide
ZW01: TestPoint; PinHeader_1x01_P2.54mm_Vertical

Connections:
+5V: C56.1, L03.2
+18V: C53.1, I54.3 (VI), I55.8 (VCC+), PM03.2, R78.1, T12.1 (E), ZW01.1
GND: C53.2, C54.2, C55.2, C56.2, D07.2 (A), I54.2 (GND), I55.4 (VCC-), PM03.1
unnamed: C54.1, I54.1 (VO), R81.1
unnamed: C55.1, I55.2 (IN+), R80.2, R83.1
unnamed: D07.1 (K), L02.1, T12.3 (C)
unnamed: I55.3 (IN-), R81.2
unnamed: I55.7 (COL_OUT), R79.2, R80.1
unnamed: L02.2, L03.1, R83.2
unnamed: R78.2, R79.1, T12.2 (B)

Notes on the sheet:
Masse au centre
14,5V
Trous de montage
17,4V
14.5V
Fixations à la coque
Passages pour l'assemblage de la coque
