sporniket/kicad-conversions--thomson-mo5--v1/subsheet_108.kicad_sch

## KiCad design subsheet_108.kicad_sch (2024-12-30, an earlier design)

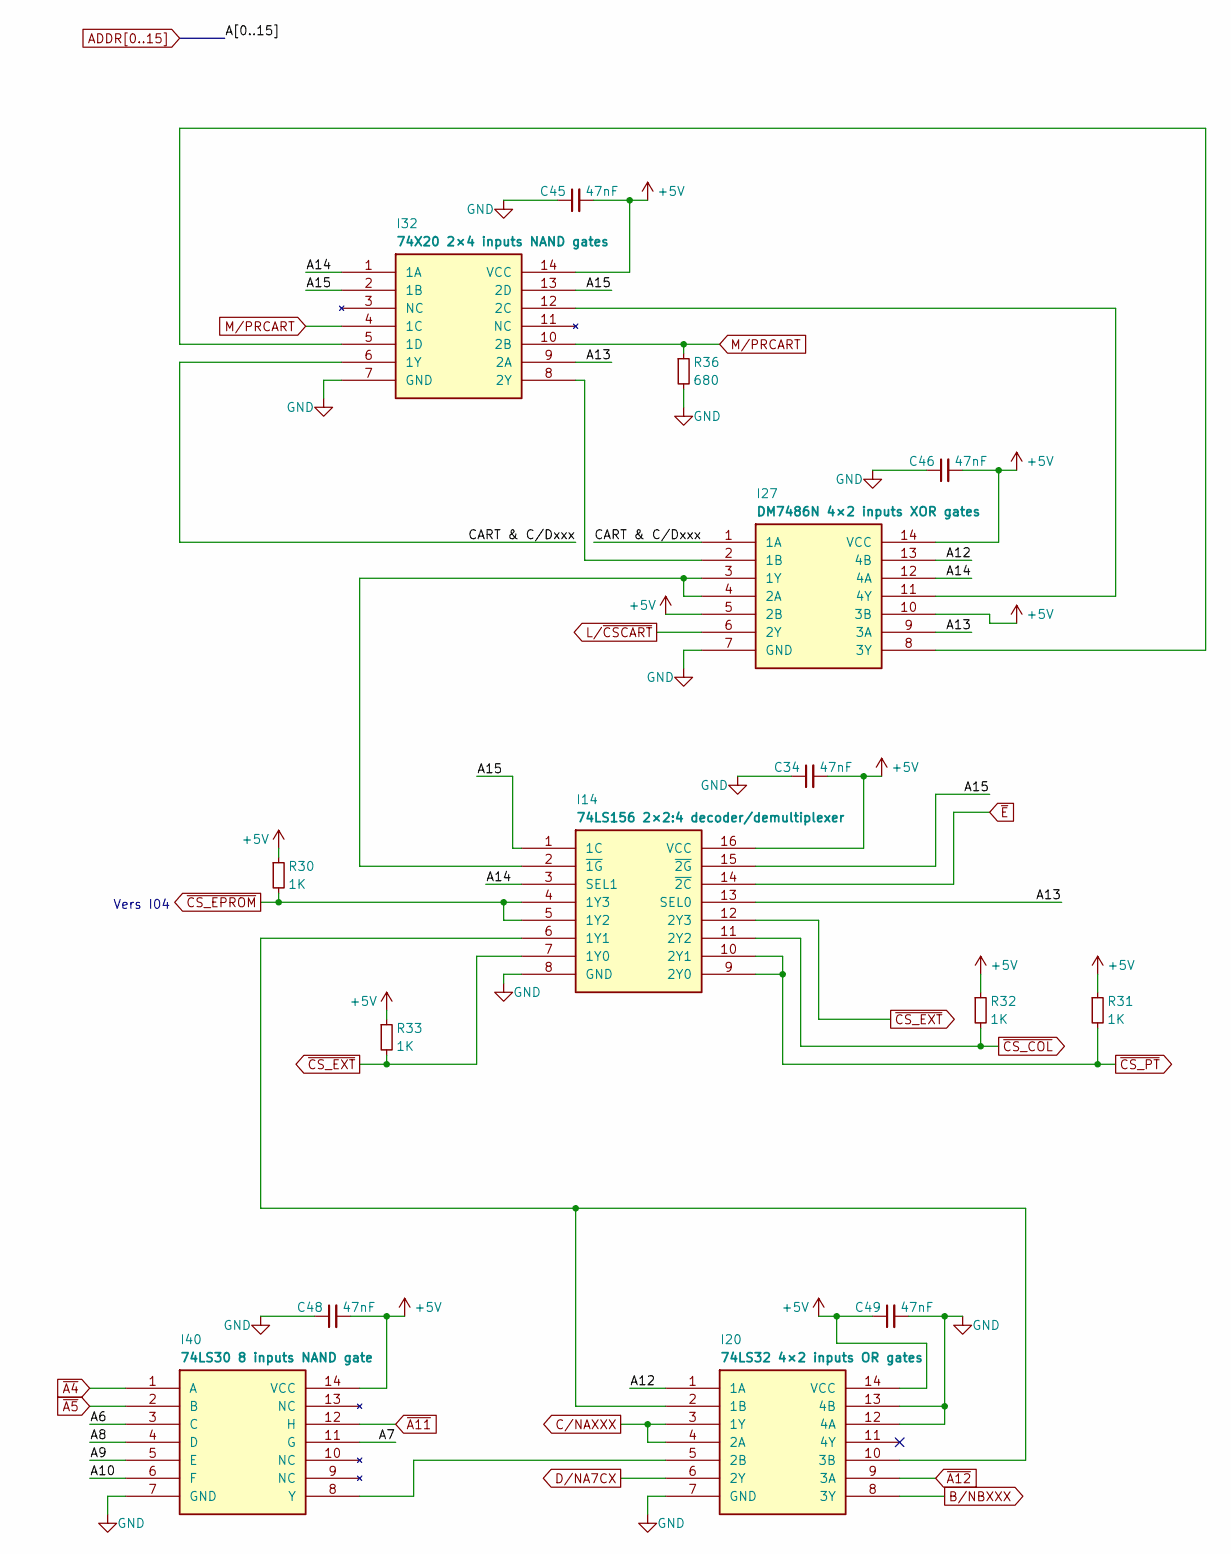
[picture p34: schematic subsheet_108.kicad_sch]

Parts:
C34, C45, C46, C48, C49: 47nF; Passive_THT_capacitor_mlcc_W2.54mm_L5.08mm
I14: 74LS156 2×2:4 decoder/demultiplexer; DIP-16_W7.62mm_LongPads
I20: 74LS32 4×2 inputs OR gates; DIP-14_W7.62mm_LongPads
I27: DM7486N 4×2 inputs XOR gates; DIP-14_W7.62mm_LongPads
I32: 74X20 2×4 inputs NAND gates; DIP-14_W7.62mm_LongPads
I40: 74LS30 8 inputs NAND gate; DIP-14_W7.62mm_LongPads
R30, R31, R32, R33: 1K; Passive_THT_resistor_EU_W2.54mm_L12.70mm
R36: 680; Passive_THT_resistor_EU_W2.54mm_L12.70mm

Connections:
+5V: C34.2, C45.2, C46.2, C48.2, C49.1, I14.16 (VCC), I20.14 (VCC), I27.5 (2B), I27.10 (3B), I27.14 (VCC), I32.14 (VCC), I40.14 (VCC), R30.1, R31.1, R32.1, R33.1
A6: I40.3 (C)
A7: I40.11 (G)
A8: I40.4 (D)
A9: I40.5 (E)
A10: I40.6 (F)
A12: I20.1 (1A), I27.13 (4B)
A13: I14.13 (SEL0), I27.9 (3A), I32.9 (2A)
A14: I14.3 (SEL1), I27.12 (4A), I32.1 (1A)
A15: I14.1 (1C), I14.15 (~2G), I32.2 (1B), I32.13 (2D)
B/NBXXX: I20.8 (3Y)
CART & C/Dxxx: I27.1 (1A), I32.6 (1Y)
C/NAXXX: I20.3 (1Y), I20.4 (2A)
D/NA7CX: I20.6 (2Y)
GND: C34.1, C45.1, C46.1, C48.1, C49.2, I14.8 (GND), I20.7 (GND), I20.12 (4A), I20.13 (4B), I27.7 (GND), I32.7 (GND), I40.7 (GND), R36.2
L/~CSCART: I27.6 (2Y)
M/PRCART: I32.4 (1C), I32.10 (2B), R36.1
unnamed: I14.2 (~1G), I27.3 (1Y), I27.4 (2A)
unnamed: I14.6 (1Y1), I20.2 (1B), I20.10 (3B)
unnamed: I20.5 (2B), I40.8 (Y)
unnamed: I27.2 (1B), I32.8 (2Y)
unnamed: I27.8 (3Y), I32.5 (1D)
unnamed: I27.11 (4Y), I32.12 (2C)
~A4: I40.1 (A)
~A5: I40.2 (B)
~A11: I40.12 (H)
~A12: I20.9 (3A)
~CS_COL: I14.11 (2Y2), R32.2
~CS_EPROM: I14.4 (1Y3), I14.5 (1Y2), R30.2
~CS_EXT: I14.7 (1Y0), I14.12 (2Y3), R33.2
~CS_PT: I14.9 (2Y0), I14.10 (2Y1), R31.2
~E: I14.14 (~2C)

Notes on the sheet:
Vers I04
